JackSabine/Breadboard_CPU/SPICE/DL_vs_TTL.asc

D1: diode; 1SR154-400
D2: diode; 1SR154-400
Q1: npn; 2N2222
Q2: npn; 2N2222
R1: res; 10k
R2: res; 10k
R3: res; 10k
R4: res; 10k
V1: voltage; 5
V2: voltage; 5
V3: voltage; 5
V4: voltage; 5
V5: voltage; 5
Named nets: 0
.tran 0 1m 0 1u
