JackSabine/Breadboard_CPU/SPICE/NegativePulse.asc

C1: cap; 0.1µ
C2: cap; 1p
Q1: npn; 2N2222
R1: res; 100
R2: res; 1k
R3: res; 1k
V1: voltage; {Vvar}
V2: voltage; PULSE(0 5 10u 1n 1n 100u 600u 10)
Named nets: Vo, 0
.tran 0 2400u 0 10n
.step param Vvar list 5 3.3
