JackSabine/Breadboard_CPU/Programming/Programs/Budgetlake.h

// Trap table
#define SLEEP           0x00
#define SPRINT          0x01
#define DISPLAY_RST     0x02

// Port registers
#define PADIR           0x00    // Not implemented in hardware
#define PBDIR           0x01
#define PORTA           0x02
#define PORTB           0x03
